qawse3dr/bam-box/CdReader.hpp

/*
 * Copyright (C) 2025 Larry Milne (https://www.larrycloud.ca)
 *
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
 * THE SOFTWARE IS PROVIDED "AS IS", WITHOUT WARRANTY OF ANY KIND, EXPRESS OR
 * IMPLIED, INCLUDING BUT NOT LIMITED TO THE WARRANTIES OF MERCHANTABILITY,
 * FITNESS FOR A PARTICULAR PURPOSE AND NONINFRINGEMENT. IN NO EVENT SHALL THE
 * AUTHORS OR COPYRIGHT HOLDERS BE LIABLE FOR ANY CLAIM, DAMAGES OR OTHER
 * LIABILITY, WHETHER IN AN ACTION OF CONTRACT, TORT OR OTHERWISE, ARISING FROM,
 * OUT OF OR IN CONNECTION WITH THE SOFTWARE OR THE USE OR OTHER DEALINGS IN THE
 * SOFTWARE.
 */
#pragma once

#include <sys/dcmd_cam.h>

#include <chrono>
#include <condition_variable>
#include <functional>
#include <mutex>
#include <string>
#include <vector>

#include "BamBoxError.hpp"
#include "BamBoxConfig.hpp"

namespace bambox {

class CdReader {
 public:
  struct Song {
    std::chrono::seconds length_ = std::chrono::seconds(0);
    std::string title_{};
    std::string artist_{};
    uint64_t start_lba_ = 0;
    /// Last sector of the track (inclusive).
    uint64_t end_lba_ = 0;
    uint8_t track_num_ = 0;
  };

  struct CD {
    std::string title_ = "Untitled";
    std::string artist_ = "Untitled";
    std::string genre_ = "Unknown";
    std::string release_id_{};
    std::string album_art_path_{};
    std::string release_date_ = "Unknown";
    uint64_t sectors_ = 0;
    /// Audio tracks only; data tracks are not represented here, so a track's
    /// position in this vector is NOT its CD track number. Use index_of_track().
    std::vector<Song> songs_{};
    uint64_t lout_track_lba_ = 0;

    /// @return index into songs_ of the given CD track number, or -1 if that
    ///         track number isn't an audio track on this disc.
    int index_of_track(uint8_t track_num) const {
      for (size_t i = 0; i < songs_.size(); i++) {
        if (songs_[i].track_num_ == track_num) {
          return static_cast<int>(i);
        }
      }
      return -1;
    }
  };

  enum class State { STOPPED, PLAYING, STOPPING };

  /**
   * @brief callback used to send data from a track.
   *
   * @param std::chrono::seconds current progress in song
   * @param void*                Song data
   * @param int                  how many frames are contained in the data (note
   * this doesn't mean the length)
   */
  using SongDataCallback = std::function<int(std::chrono::seconds, void *, int)>;

  // Time, data, frames (todo maybe this should be a vector)
  struct AudioData {
    std::chrono::seconds ts;
    int frames;
    std::array<uint8_t, CDROM_CDDA_FRAME_SIZE> data;
  };

 private:
 BamBoxConfig cfg_{};
  std::string mount_point_;
  CD current_cd_{};
  int handle_ = -1;

  // The LBA info of a track.
  // Only should be considered value when state_ is PLAYING or PAUSED
  uint32_t track_lba_start_ = 0;
  uint32_t track_lba_current_ = 0;
  uint32_t track_lba_end_ = 0;
  uint32_t track_num_ = 0;

  constexpr static int OP_RETRY_COUNT = 3;
  constexpr static std::chrono::milliseconds OP_RETRY_TIMEOUT = std::chrono::milliseconds(100);

 public:
  CdReader(const BamBoxConfig& cfg);
  ~CdReader();

  Error eject();
  Error load();

  /// Updates the disc info from the web or local cache.
  /// @param force True to update the online metadata no matter if it is already cached
  Error update_disc_info(bool force = false);
  Error wait_for_disc();
  bool has_disc();

  Error read(CdReader::AudioData &data);
  Error set_position(uint8_t track_num, uint32_t lba_offset = 0);

  const CD &get_disc() const { return current_cd_; }
  const Song &get_current_song() const { return current_cd_.songs_[track_num_ - 1]; }

  uint32_t get_track_current_lba() const { return track_lba_current_; }
  uint32_t get_track_start_lba() const { return track_lba_start_; }
  uint32_t get_track_number() const { return track_num_; }

  static std::string get_disc_id(const CD& cd);
  static std::string get_freedb_id(const CD& cd);
};
}  // namespace bambox
