qawse3dr/bam-box/CdPlayer.cpp

/*
 * Copyright (C) 2025 Larry Milne (https://www.larrycloud.ca)
 *
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
 * THE SOFTWARE IS PROVIDED "AS IS", WITHOUT WARRANTY OF ANY KIND, EXPRESS OR
 * IMPLIED, INCLUDING BUT NOT LIMITED TO THE WARRANTIES OF MERCHANTABILITY,
 * FITNESS FOR A PARTICULAR PURPOSE AND NONINFRINGEMENT. IN NO EVENT SHALL THE
 * AUTHORS OR COPYRIGHT HOLDERS BE LIABLE FOR ANY CLAIM, DAMAGES OR OTHER
 * LIABILITY, WHETHER IN AN ACTION OF CONTRACT, TORT OR OTHERWISE, ARISING FROM,
 * OUT OF OR IN CONNECTION WITH THE SOFTWARE OR THE USE OR OTHER DEALINGS IN THE
 * SOFTWARE.
 */

#include "CdPlayer.hpp"

#include <spdlog/spdlog.h>

using bambox::CdPlayer;
using bambox::Error;

CdPlayer::CdPlayer(const std::shared_ptr<CdReader>& reader, std::shared_ptr<AudioPlayer>& audio_player,
                   EventCB event_cb)
    : reader_(reader), audio_player_(audio_player), event_cb_(event_cb) {}

Error CdPlayer::start() {
  cd_loader_loop_ = std::thread(&CdPlayer::cd_loader_loop, this);
  return {};
}

Error CdPlayer::load() {
  Error res;
  while (true) {
    // Wait for media rather than spinning on open()/devctl() at full tilt.
    if (!reader_->has_disc()) {
      reader_->wait_for_disc();
      continue;
    }

    {
      std::unique_lock<std::mutex> lk(mtx_);
      res = reader_->load();
    }
    if (res.is_ok()) {
      break;
    }

    spdlog::info("load result: {}", res.str());
    std::this_thread::sleep_for(std::chrono::milliseconds(500));
  }

  event_cb_(Event::CD_LOADED, reader_->get_disc());
  return res;
}

Error CdPlayer::play() {
  spdlog::info("CdPlayer::play()");
  std::lock_guard<std::mutex> lk(mtx_);
  if (state_ != State::STOPPED) {
    spdlog::info("CdPlayer::play err()");

    return {ECode::ERR_INVAL_STATE, "CdPlayer cannot be started, already running"};
  }
  // Clean up any old threads.
  if (cd_reader_loop_.joinable()) {
    cd_reader_loop_.join();
  }
  state_ = State::PLAYING;
  cd_reader_loop_ = std::thread(&CdPlayer::cd_reader_loop, this);
  spdlog::info("CdPlayer::play rtn()");

  return {};
}

Error CdPlayer::pause() {
  std::unique_lock<std::mutex> lk(mtx_);
  if (state_ != State::PLAYING) {
    return {ECode::ERR_INVAL_STATE, "CdPlayer cannot be stopped, not running"};
  }
  state_ = State::STOPPING;

  // Briefly unlock to join the cd loop.
  lk.unlock();
  if (cd_reader_loop_.joinable()) {
    cd_reader_loop_.join();
  }
  lk.lock();
  state_ = State::STOPPED;
  return {};
}

void CdPlayer::cd_reader_loop() {
  CdReader::AudioData data = {.frames = 0};
  std::chrono::seconds prev_sec(1000000000);
  Error err{};
  while (1) {
    // Lock when reading from the cd player to avoid threading issues.
    for (int i = 0; i < 5; i++) {
      std::lock_guard<std::mutex> lk(mtx_);
      // Stop requested.
      if (state_ == State::STOPPING) {
        return;
      }
      err = reader_->read(data);
      if (err.is_ok()) {
        break;
      }
    }
    // No read the message outside of the lock checking the contents for any callbacks.

    if (err.is_ok() && data.frames == EOF) {
      // notify the track ended but keep reading, this assumes that the event_cb_ will update the reader
      EventData event_data(0);
      event_cb_(Event::CD_TRACK_ENDED, event_data);
      continue;
    }

    if (err.is_error()) {
      {
        std::lock_guard<std::mutex> lk(mtx_);
        state_ = State::STOPPED;
      }
      EventData event_data(err);
      event_cb_(Event::CD_EJECTED, event_data);
      return;
    }

    auto ret = audio_player_->write(data.data.data(), data.frames);
    if (ret < 0) {
      spdlog::warn("Failed to write audio: {}", ret);
    }

    // Update time after write as it is more important. Also only update if seconds actually changed, to avoid spam.
    if (prev_sec != data.ts) {
      event_cb_(Event::CD_TIME_UPDATE, data.ts);
      prev_sec = data.ts;
    }
  }
}

void CdPlayer::cd_loader_loop() {
  EventData event_data(0);
  event_cb_(CdPlayer::Event::STARTUP, event_data);
  // while(1) {}
}
